i-Saac-IV/verbum-horologium/photos/DSC00016.jpg

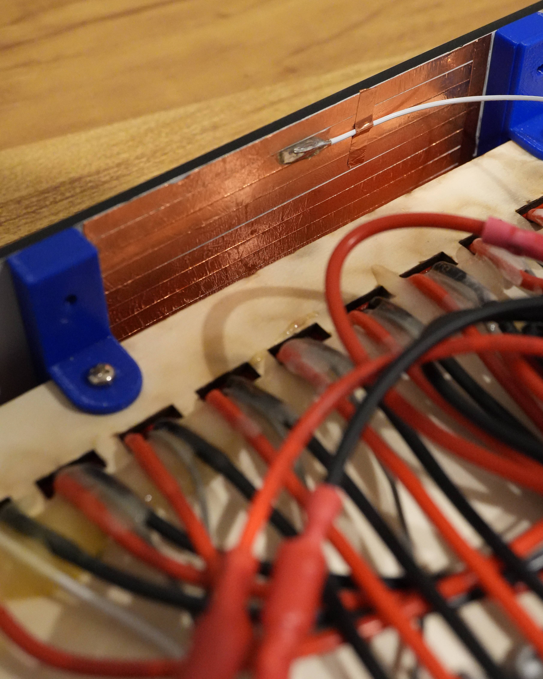
photos/DSC00016.jpg
