i-Saac-IV/verbum-horologium/photos/DSC00032.jpg

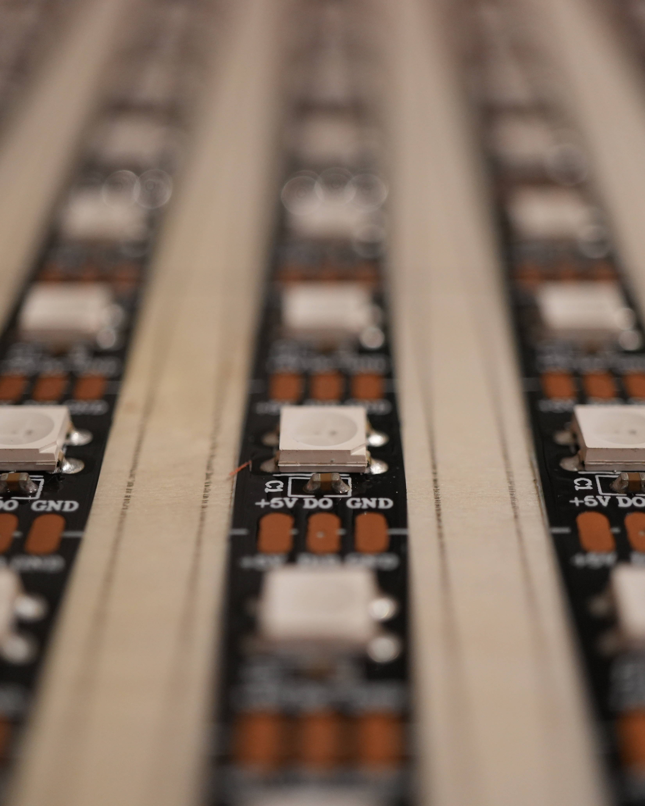
photos/DSC00032.jpg
