i-Saac-IV/verbum-horologium/photos/DSC00034.jpg

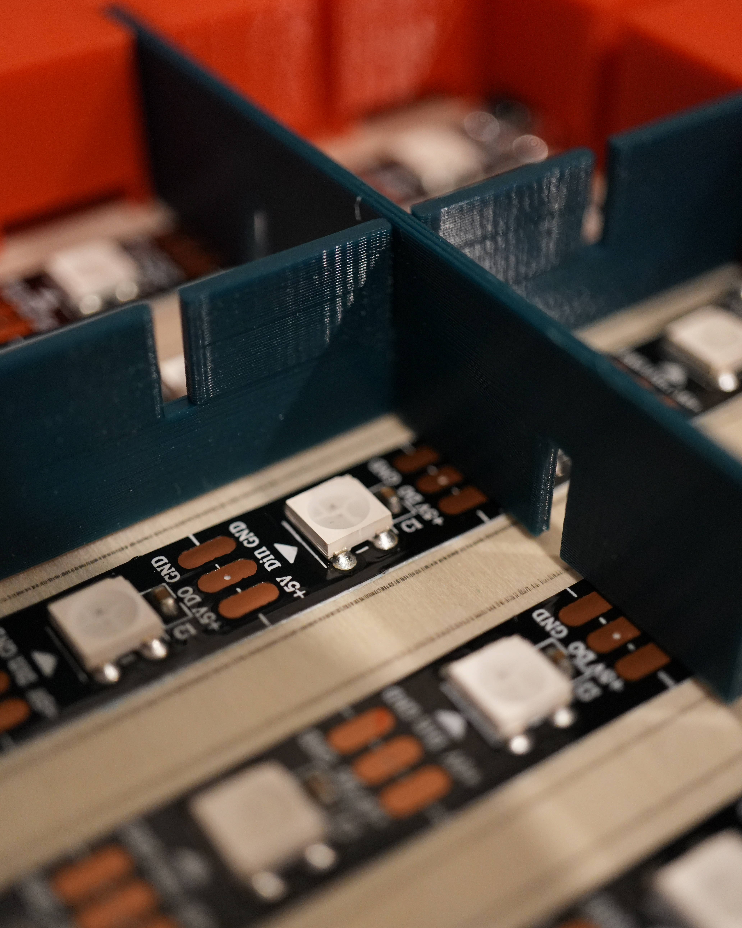
photos/DSC00034.jpg
