i-Saac-IV/verbum-horologium/photos/DSC00037.jpg

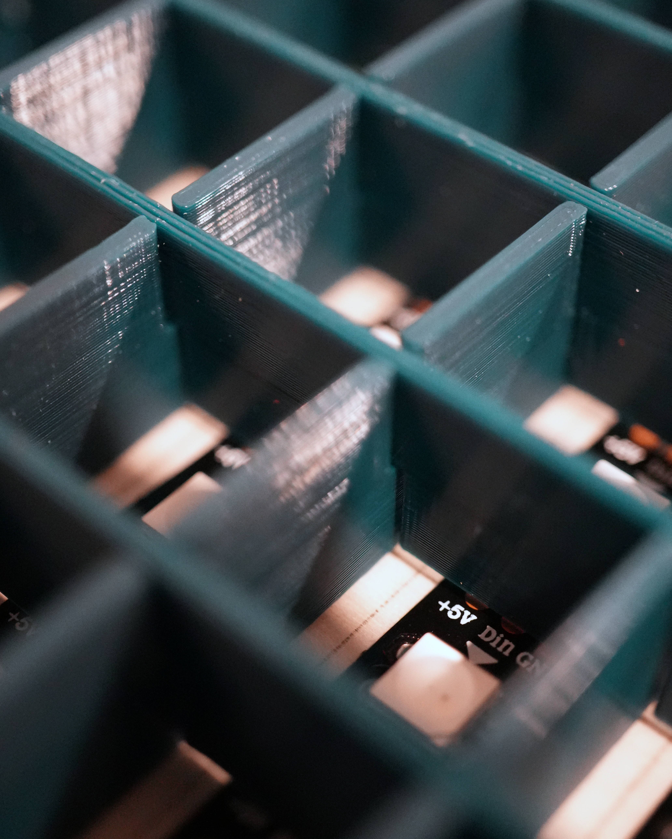
photos/DSC00037.jpg
