i-Saac-IV/verbum-horologium/photos/DSC00046.jpg

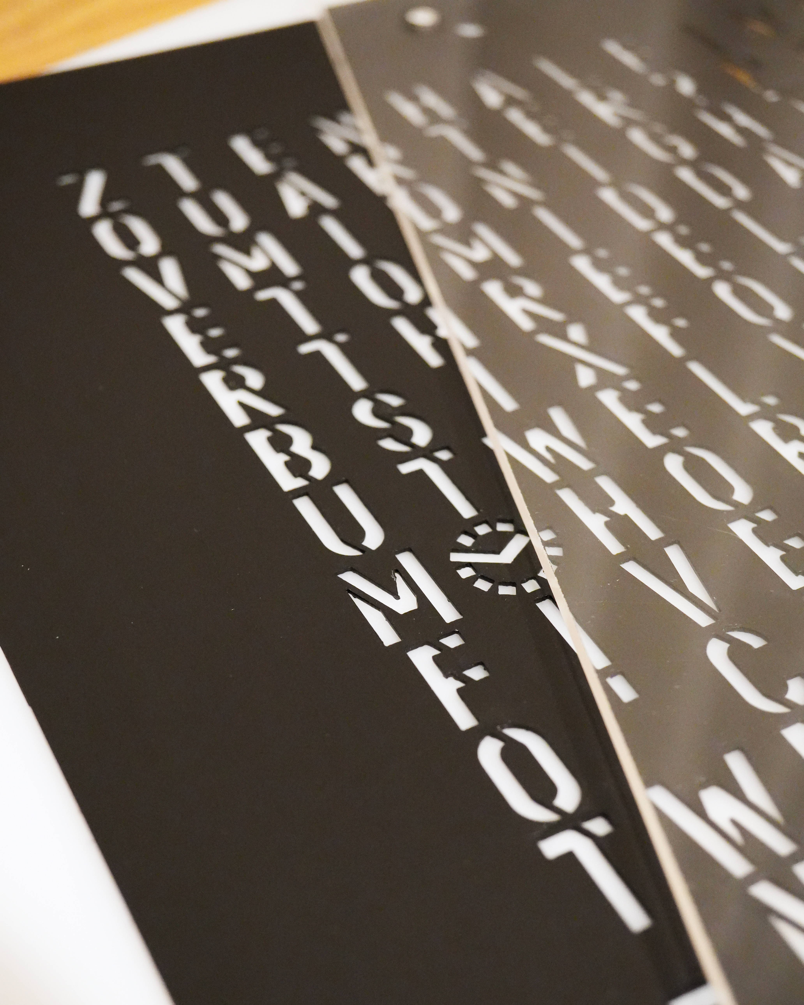
photos/DSC00046.jpg
