i-Saac-IV/verbum-horologium/photos/DSC00053.jpg

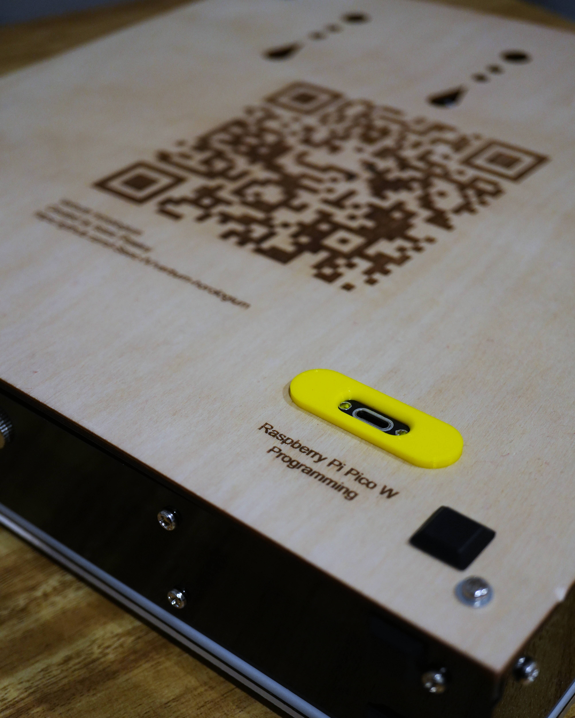
photos/DSC00053.jpg
