i-Saac-IV/verbum-horologium/photos/DSC00057.jpg

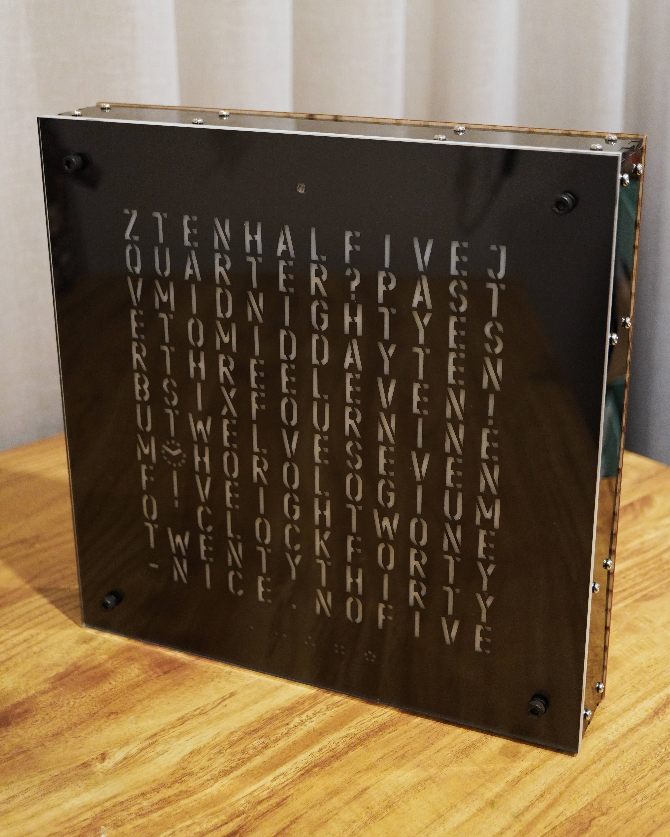
photos/DSC00057.jpg
