i-Saac-IV/verbum-horologium/photos/DSC00059.jpg

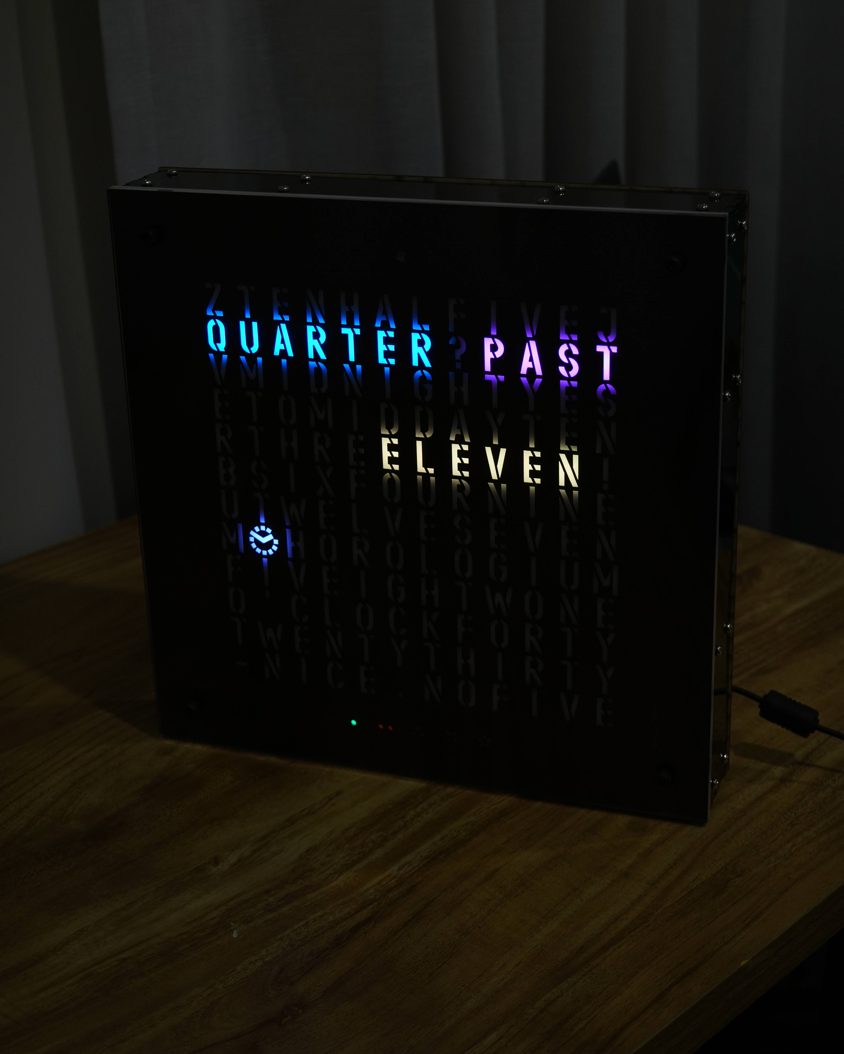
photos/DSC00059.jpg
