i-Saac-IV/verbum-horologium/photos/DSC00060.jpg

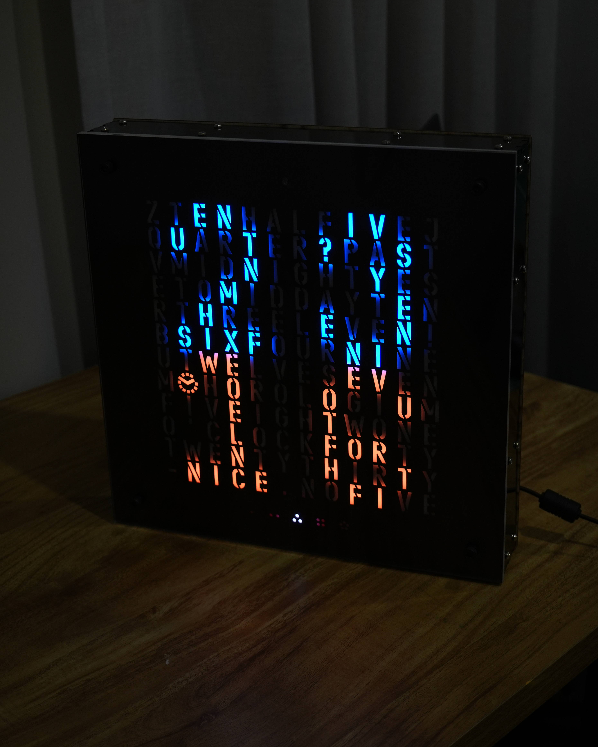
photos/DSC00060.jpg
